generot/cerebralink/kicad-schematics/BCI.kicad_sch

## KiCad design kicad-schematics/BCI.kicad_sch (2023-05-29)

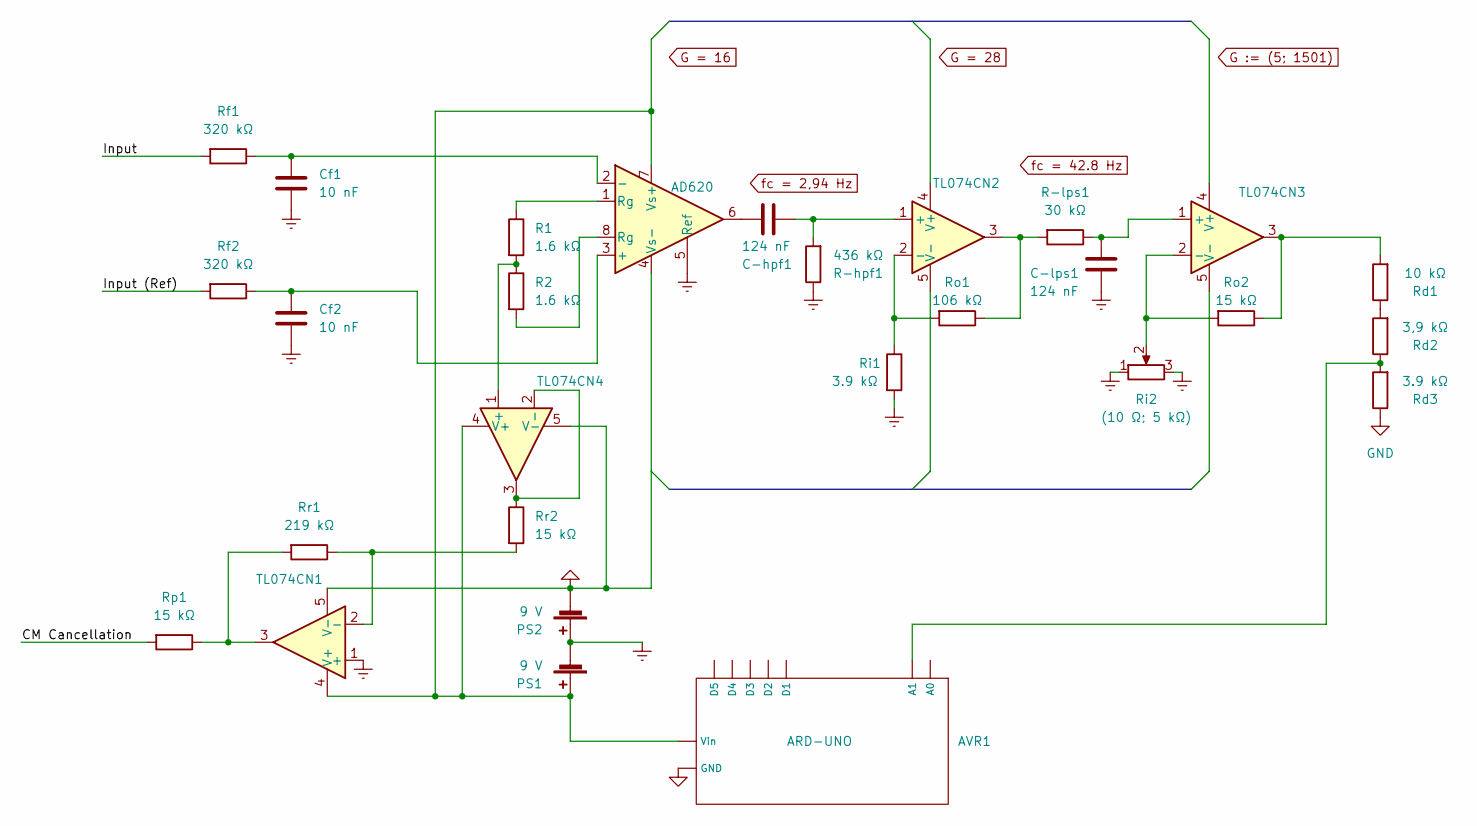
[picture p23: schematic BCI.kicad_sch]

Parts:
AVR1: ARD-UNO
C-hpf1: 124 nF; CP_Axial_L10.0mm_D4.5mm_P15.00mm_Horizontal
C-lps1: 124 nF; CP_Axial_L10.0mm_D4.5mm_P15.00mm_Horizontal
Cf1, Cf2: 10 nF; CP_Axial_L10.0mm_D4.5mm_P15.00mm_Horizontal
PS1, PS2: 9 V; BatteryHolder_TruPower_BH-331P_3xAA
R1, R2: 1.6 kΩ; R_Axial_DIN0204_L3.6mm_D1.6mm_P1.90mm_Vertical
R-hpf1: 436 kΩ; R_Axial_DIN0204_L3.6mm_D1.6mm_P1.90mm_Vertical
R-lps1: 30 kΩ; R_Axial_DIN0204_L3.6mm_D1.6mm_P1.90mm_Vertical
Rd1: 10 kΩ; R_Axial_DIN0204_L3.6mm_D1.6mm_P1.90mm_Vertical
Rd2: 3,9 kΩ; R_Axial_DIN0204_L3.6mm_D1.6mm_P1.90mm_Vertical
Rd3: 3.9 kΩ; R_Axial_DIN0204_L3.6mm_D1.6mm_P1.90mm_Vertical
Rf1, Rf2: 320 kΩ; R_Axial_DIN0204_L3.6mm_D1.6mm_P1.90mm_Vertical
Ri1: 3.9 kΩ; R_Axial_DIN0204_L3.6mm_D1.6mm_P1.90mm_Vertical
Ri2: (10 Ω; 5 kΩ)
Ro1: 106 kΩ; R_Axial_DIN0204_L3.6mm_D1.6mm_P1.90mm_Vertical
Ro2: 15 kΩ; R_Axial_DIN0204_L3.6mm_D1.6mm_P1.90mm_Vertical
Rp1: 15 kΩ; R_Axial_DIN0204_L3.6mm_D1.6mm_P1.90mm_Vertical
Rr1: 219 kΩ; R_Axial_DIN0204_L3.6mm_D1.6mm_P1.90mm_Vertical
Rr2: 15 kΩ; R_Axial_DIN0204_L3.6mm_D1.6mm_P1.90mm_Vertical
TL074CN1, TL074CN2, TL074CN3, TL074CN4: OPAMP; TL074CN
U1: AD620; AD620ANZ

Connections:
CM Cancellation: Rp1.2
Earth: C-lps1.2, Cf1.2, Cf2.2, PS1.2 (-), PS2.1 (+), R-hpf1.1, Ri1.2, Ri2.1, Ri2.3, TL074CN1.1 (+), U1.5 (Ref)
GND: AVR1., PS2.2 (-), Rd3.1, TL074CN1.5 (V-), TL074CN4.5 (V-), U1.4 (Vs-)
Input: Rf1.2
Input (Ref): Rf2.2
unnamed: AVR1., PS1.1 (+), Rd2.1, Rd3.2, TL074CN1.4 (V+), TL074CN4.4 (V+), U1.7 (Vs+)
unnamed: C-hpf1.1, R-hpf1.2, TL074CN2.1 (+)
unnamed: C-hpf1.2, U1.6
unnamed: C-lps1.1, R-lps1.1, TL074CN3.1 (+)
unnamed: Cf1.1, Rf1.1, U1.2 (-)
unnamed: Cf2.1, Rf2.1, U1.3 (+)
unnamed: R1.1, U1.1 (Rg)
unnamed: R1.2, R2.1, TL074CN4.1 (+)
unnamed: R2.2, U1.8 (Rg)
unnamed: R-lps1.2, Ro1.1, TL074CN2.3
unnamed: Rd1.1, Rd2.2
unnamed: Rd1.2, Ro2.1, TL074CN3.3
unnamed: Ri1.1, Ro1.2, TL074CN2.2 (-)
unnamed: Ri2.2, Ro2.2, TL074CN3.2 (-)
unnamed: Rp1.1, Rr1.2, TL074CN1.3
unnamed: Rr1.1, Rr2.2, TL074CN1.2 (-)
unnamed: Rr2.1, TL074CN4.2 (-), TL074CN4.3
